tonykoop/kora/cad-recovered-2026-07-04/cad/neck_cnc/neck_cnc_preview.png

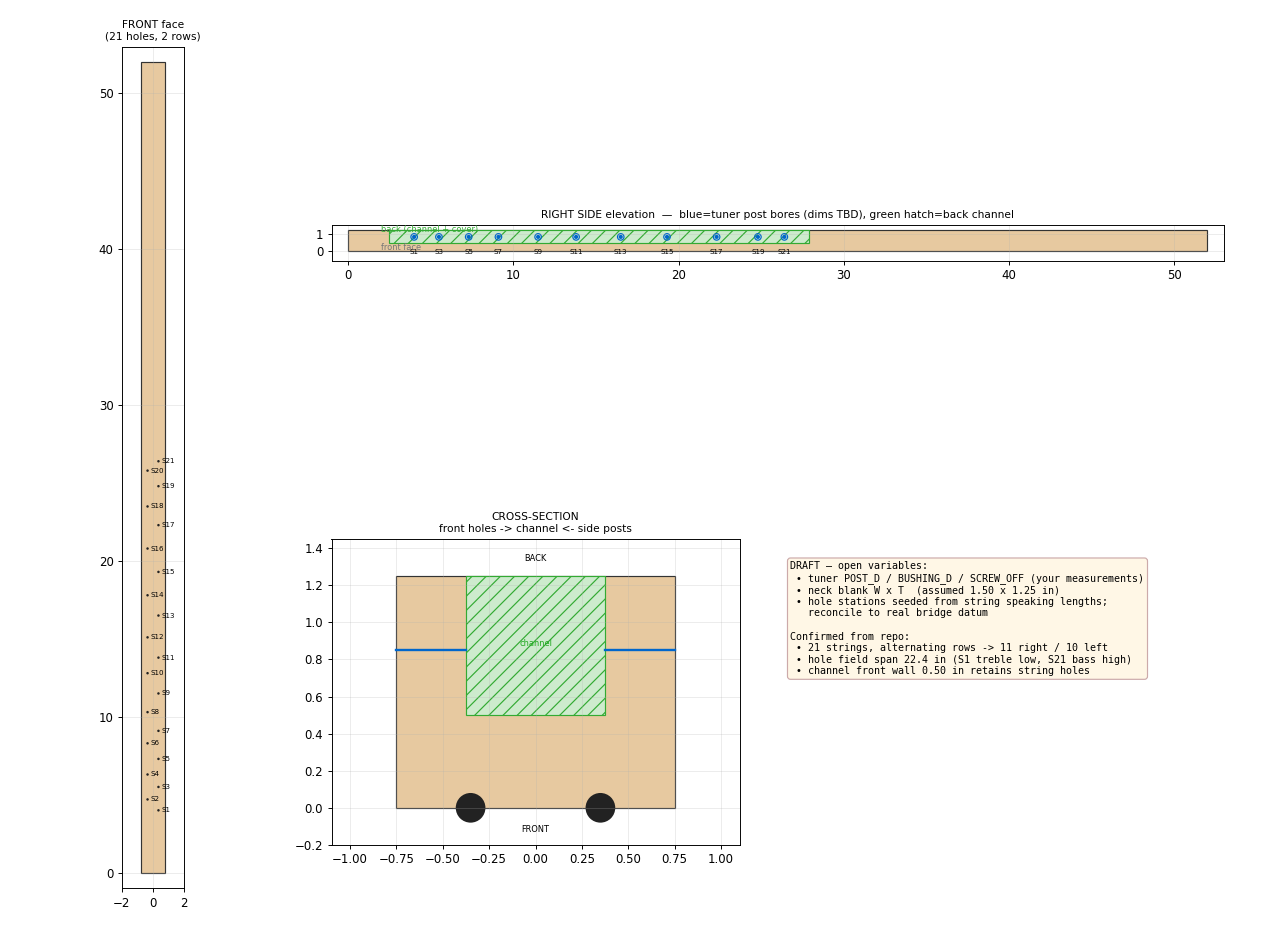
cad-recovered-2026-07-04/cad/neck_cnc/neck_cnc_preview.png
