tonykoop/kora/projects/Large 50” African Kora Style String Instrument Gourd Harp Tribal Folk Decor _ eBay_files/s-l500.jpg

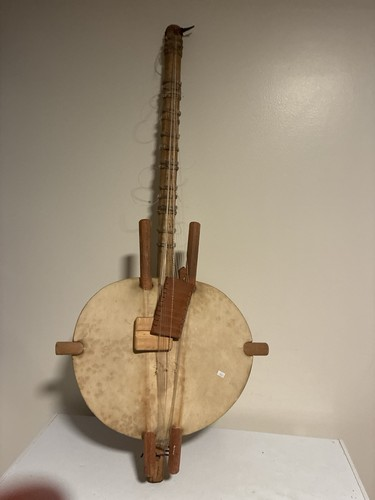
projects/Large 50” African Kora Style String Instrument Gourd Harp Tribal Folk Decor _ eBay_files/s-l500.jpg
