tonykoop/kora/projects/restoration photo album/20260529_142627.jpg

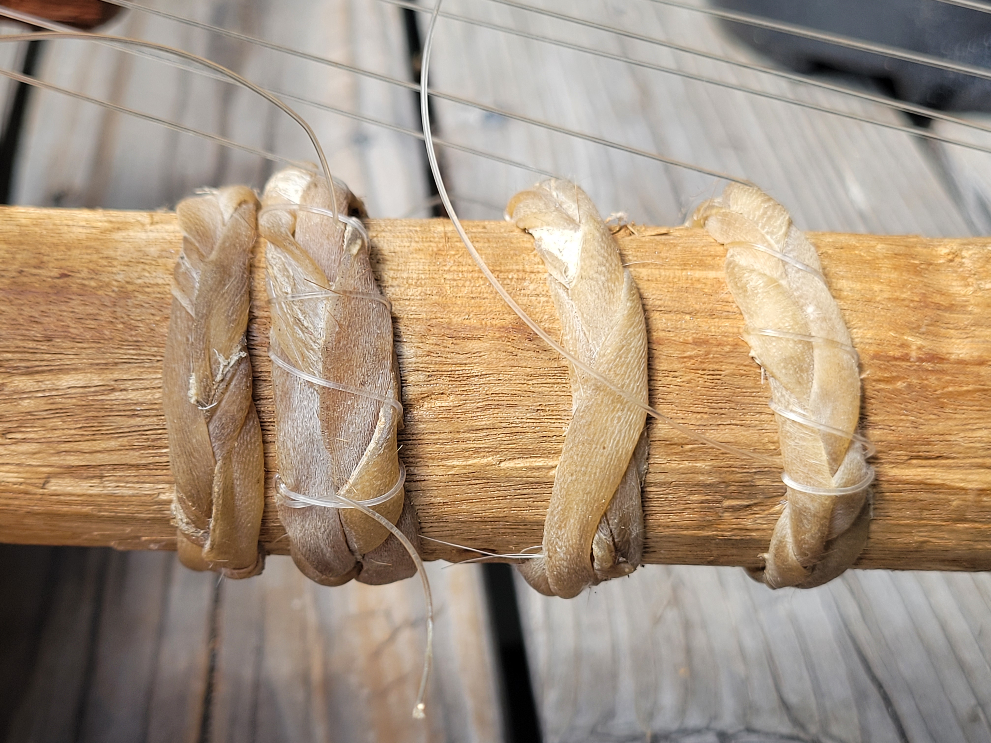
projects/restoration photo album/20260529_142627.jpg
