tonykoop/kora/projects/restoration photo album/20260529_142642.jpg

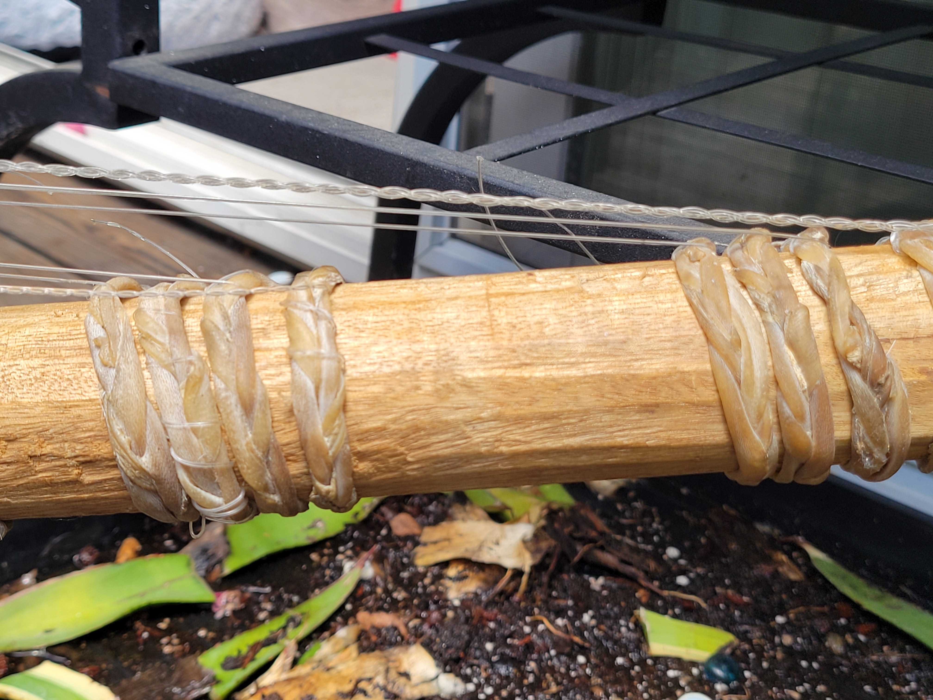
projects/restoration photo album/20260529_142642.jpg
