tonykoop/kora/projects/restoration photo album/20260529_142644.jpg

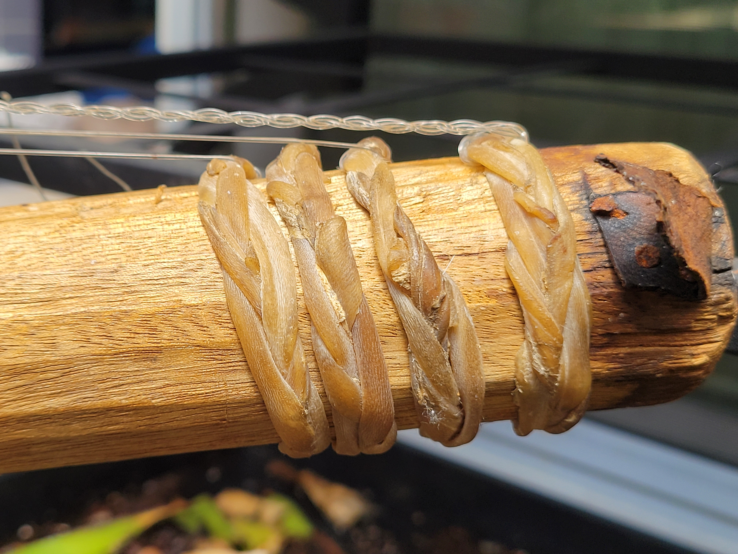
projects/restoration photo album/20260529_142644.jpg
