tonykoop/kora/projects/restoration photo album/20260529_142652.jpg

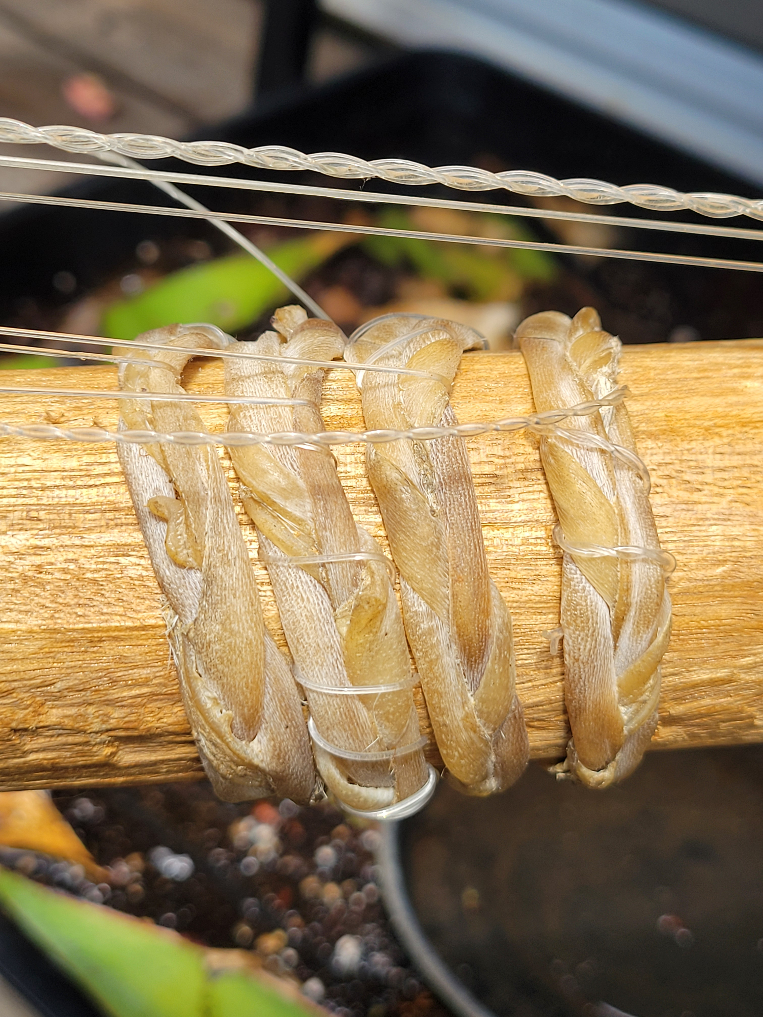
projects/restoration photo album/20260529_142652.jpg
