tonykoop/kora/projects/restoration photo album/20260529_142718.jpg

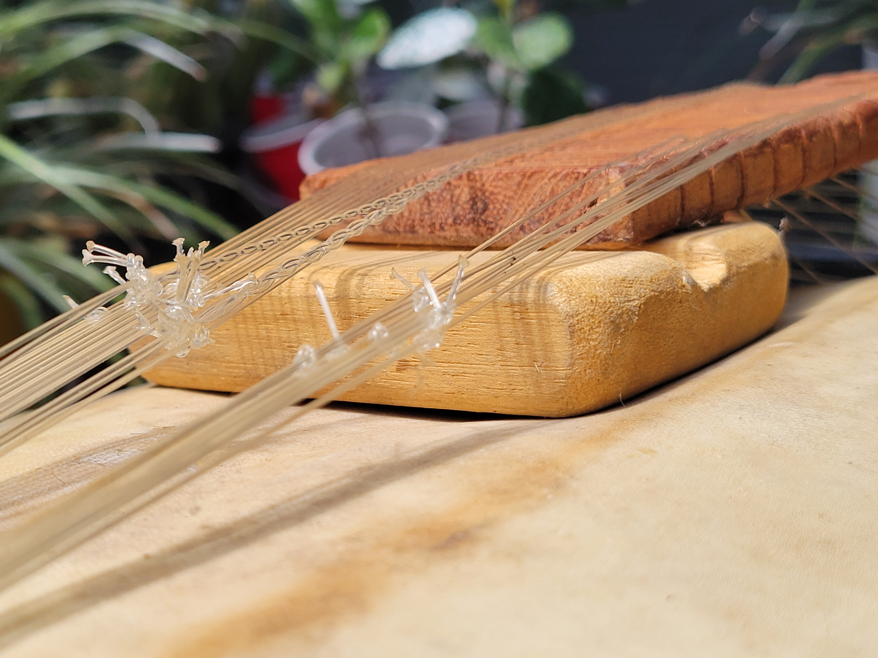
projects/restoration photo album/20260529_142718.jpg
