tonykoop/kora/projects/restoration photo album/20260529_142737.jpg

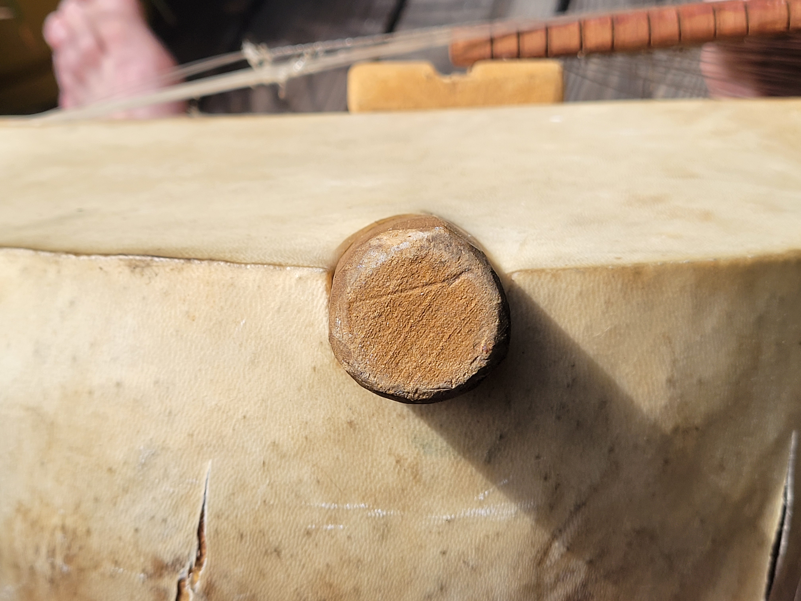
projects/restoration photo album/20260529_142737.jpg
