tonykoop/kora/projects/restoration photo album/20260529_142741.jpg

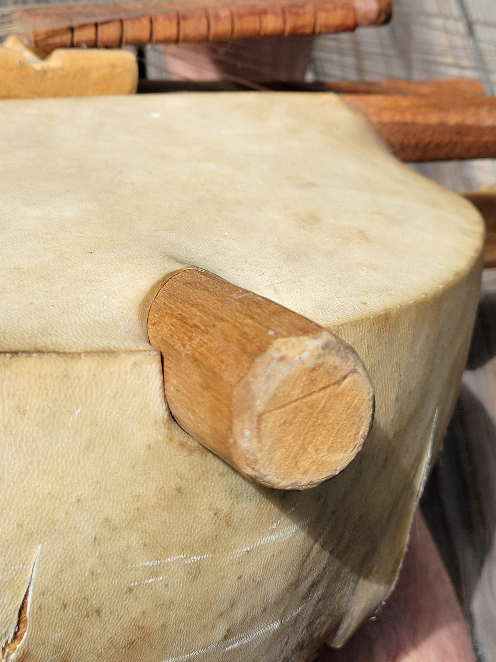
projects/restoration photo album/20260529_142741.jpg
