tonykoop/kora/projects/restoration photo album/20260529_142750.jpg

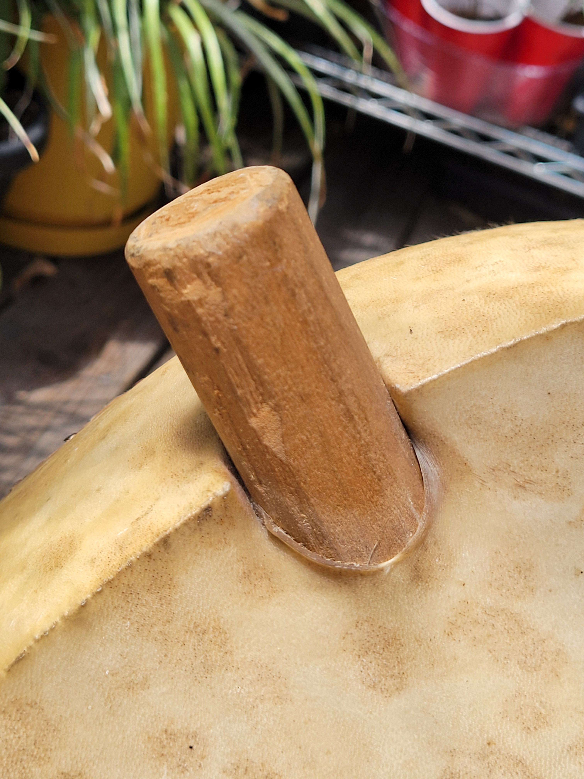
projects/restoration photo album/20260529_142750.jpg
