tonykoop/kora/projects/restoration photo album/20260529_142814.jpg

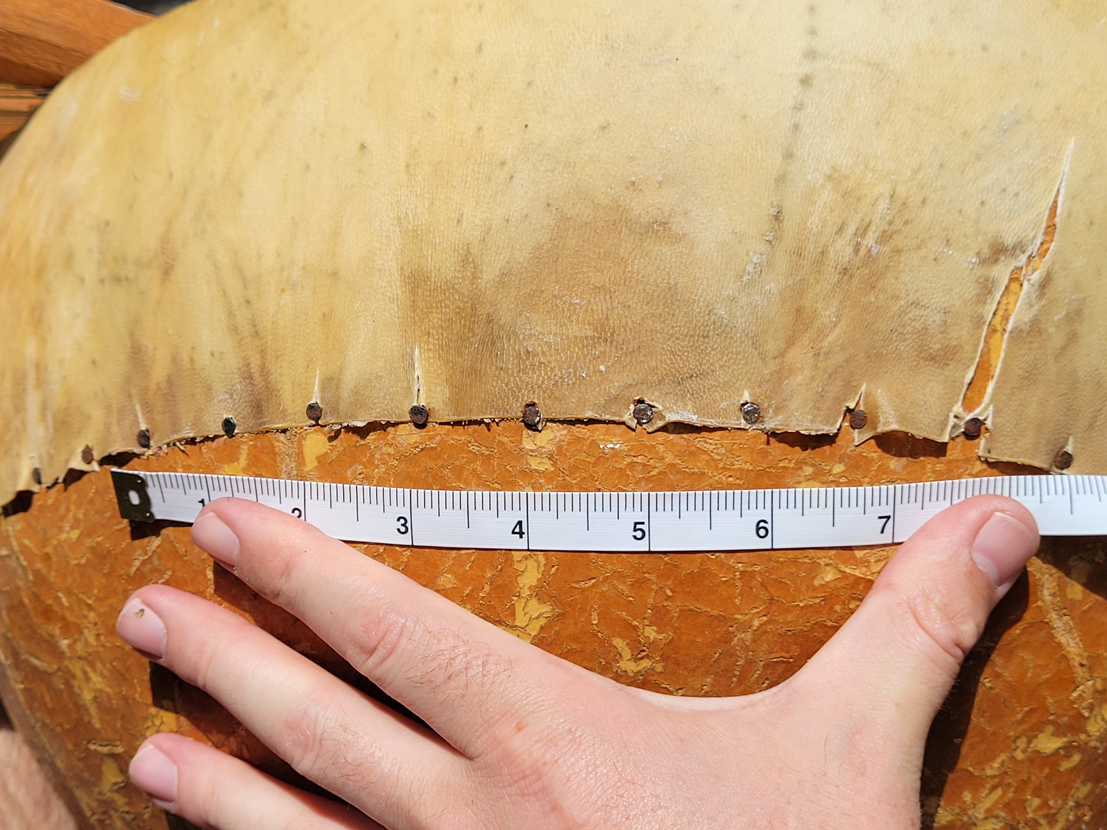
projects/restoration photo album/20260529_142814.jpg
