tonykoop/kora/projects/restoration photo album/20260529_142840.jpg

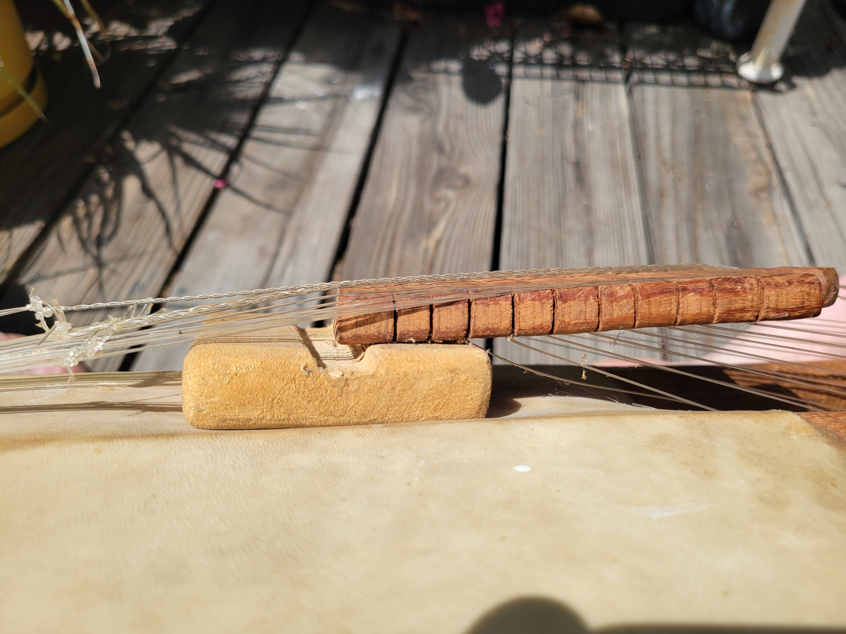
projects/restoration photo album/20260529_142840.jpg
