tonykoop/kora/projects/restoration photo album/20260529_142852.jpg

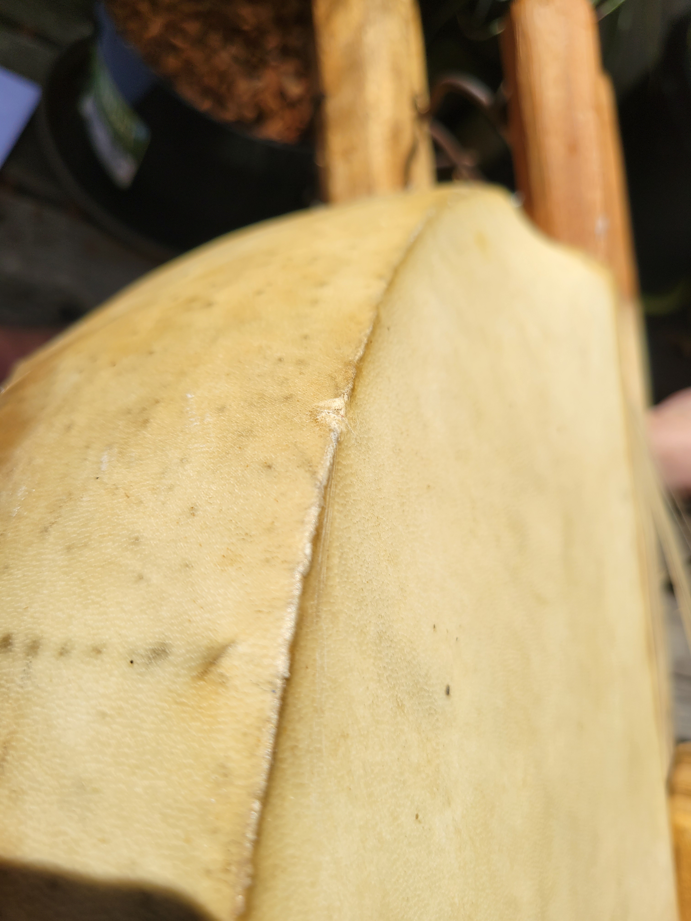
projects/restoration photo album/20260529_142852.jpg
