tonykoop/kora/projects/restoration photo album/20260529_142935.jpg

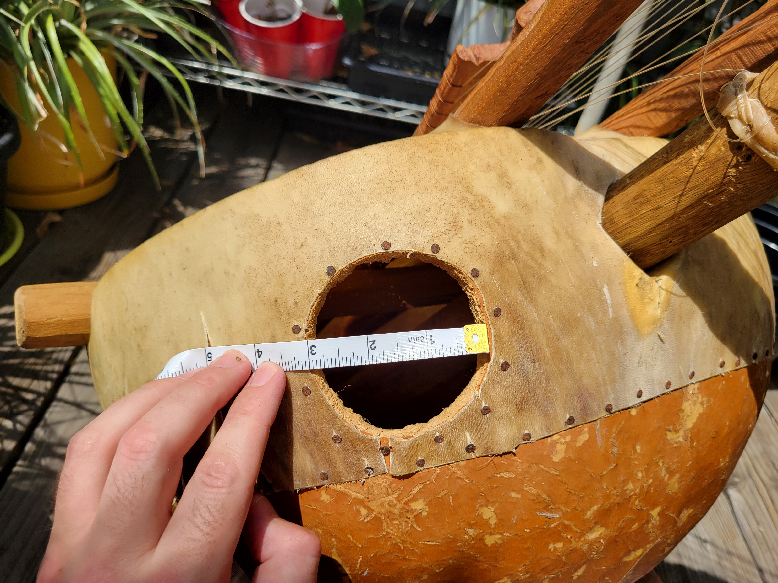
projects/restoration photo album/20260529_142935.jpg
