tonykoop/kora/projects/restoration photo album/20260529_143312.jpg

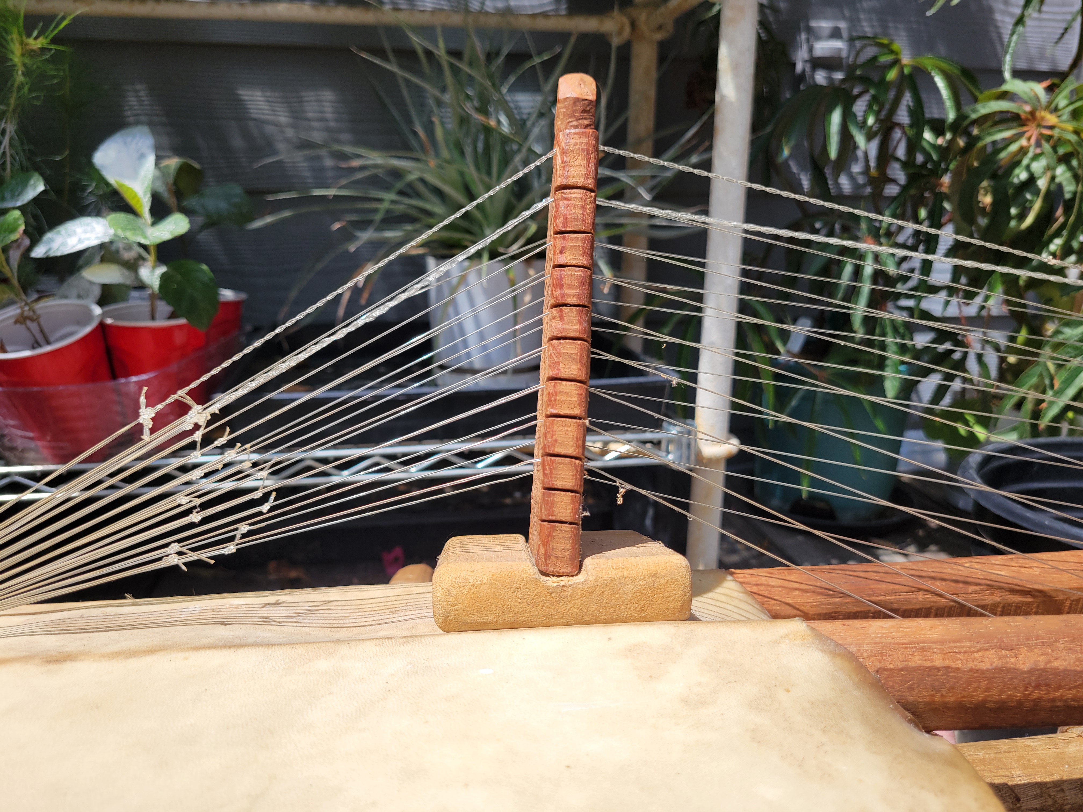
projects/restoration photo album/20260529_143312.jpg
