tonykoop/kora/cad/KOR-000-BridgePad.SLDPRT

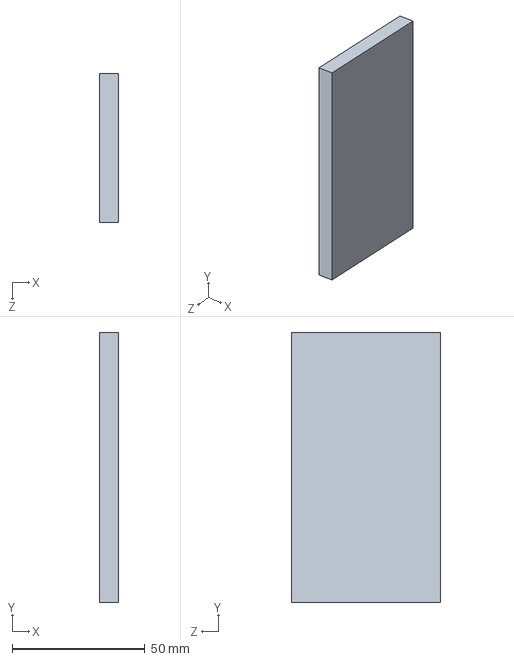
[picture p44: CAD file, 2026-07-09]
cad/KOR-000-BridgePad.SLDPRT
6.98 x 101.6 x 55.9 mm
