tonykoop/kora/cad/neck2_cnc/KOR-NECK-GlueUpV3.SLDPRT

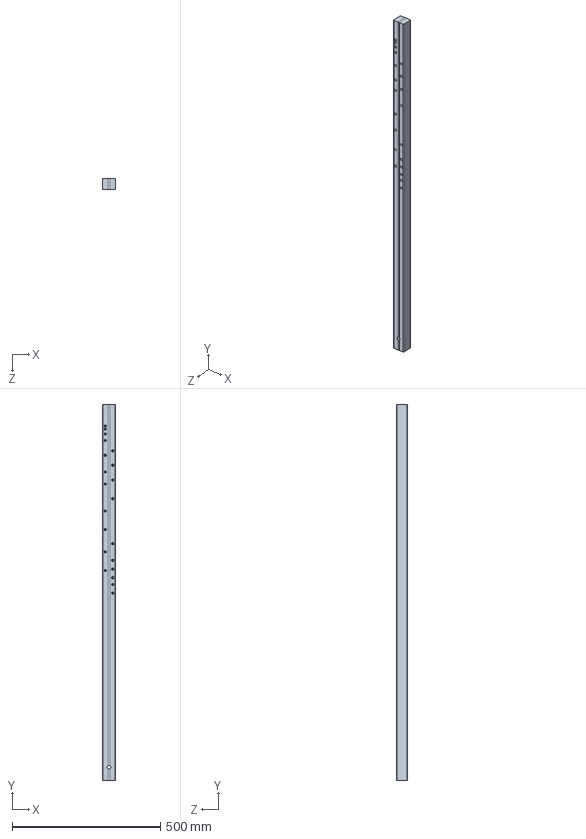
[picture p45: CAD file, 2026-07-09]
cad/neck2_cnc/KOR-NECK-GlueUpV3.SLDPRT
44.5 x 1270.0 x 38.1 mm
