tonykoop/kora/cad-recovered-2026-07-04/cad/BrassRod3-16.SLDPRT

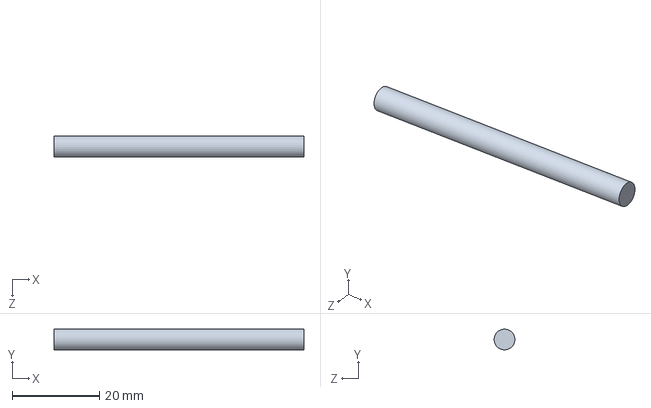
[picture p46: CAD file, 2026-07-09]
cad-recovered-2026-07-04/cad/BrassRod3-16.SLDPRT
57.1 x 4.76 x 4.76 mm
