tonykoop/kora/cad/Musiclily Pro 14mm bass string ferrule.SLDPRT

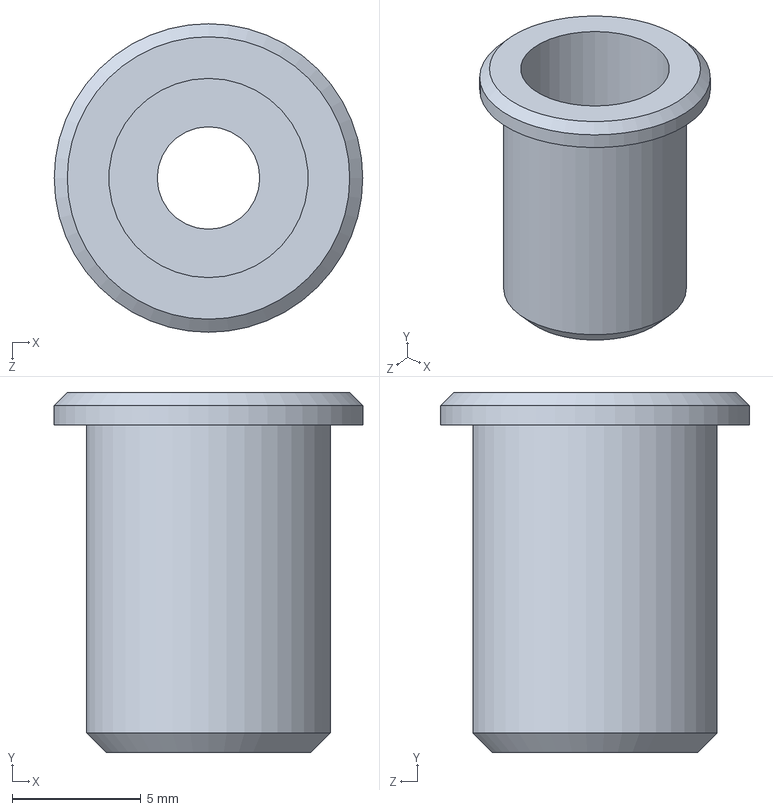
[picture p47: CAD file, 2026-07-09]
cad/Musiclily Pro 14mm bass string ferrule.SLDPRT
12.0 x 14.0 x 12.0 mm
