tonykoop/kora/cad/neck2_cnc/KOR-NECK-CENTER.SLDPRT

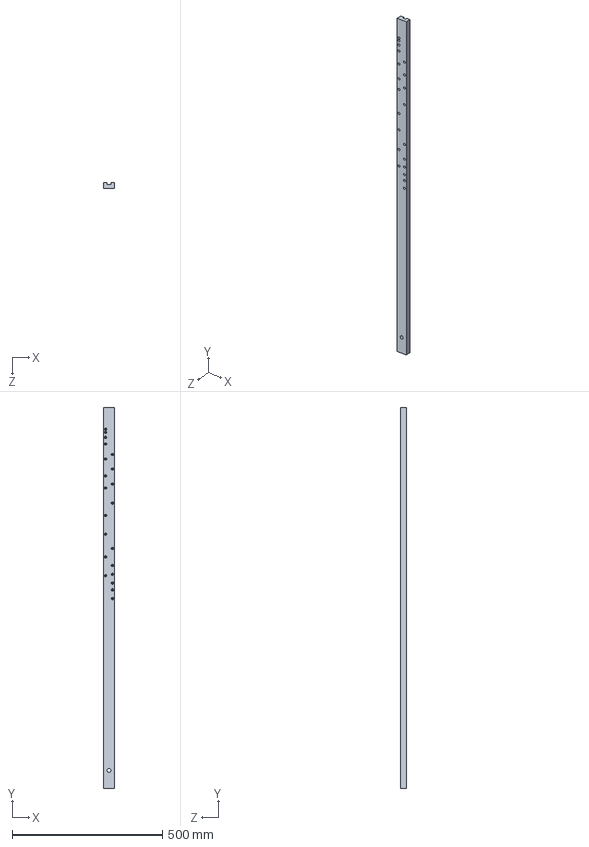
[picture p48: CAD file, 2026-07-09]
cad/neck2_cnc/KOR-NECK-CENTER.SLDPRT
38.1 x 1270.0 x 19.1 mm
