tonykoop/kora/cad-recovered-from-stash-20260518/cad/KOR-000-Gourd.SLDPRT

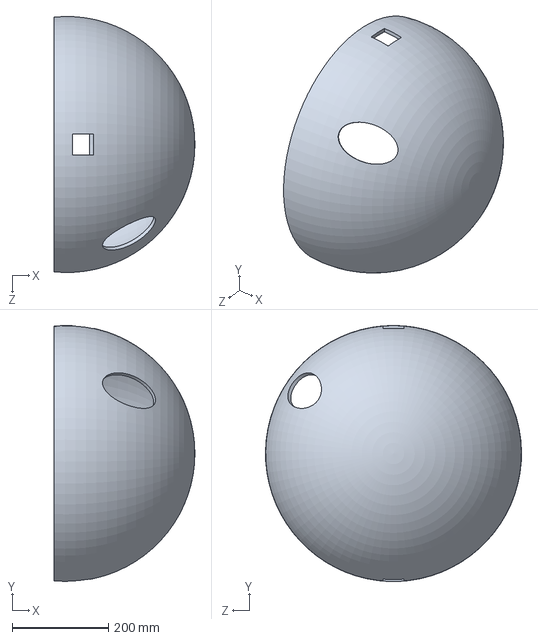
[picture p49: CAD file, 2026-05-31]
cad-recovered-from-stash-20260518/cad/KOR-000-Gourd.SLDPRT
293.4 x 533.4 x 533.2 mm
