tonykoop/kora/cad/KOR-000-Membrane.SLDPRT

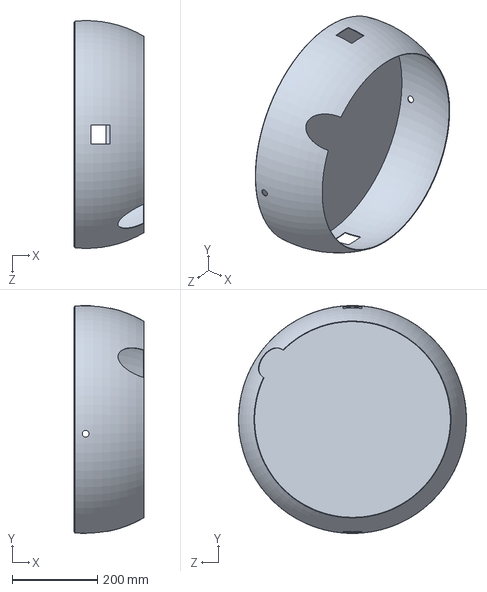
[picture p50: CAD file, 2026-07-09]
cad/KOR-000-Membrane.SLDPRT
163.6 x 536.4 x 535.9 mm
