tonykoop/kora/cad/neck2_cnc/KOR-NECK-SIDE.SLDPRT

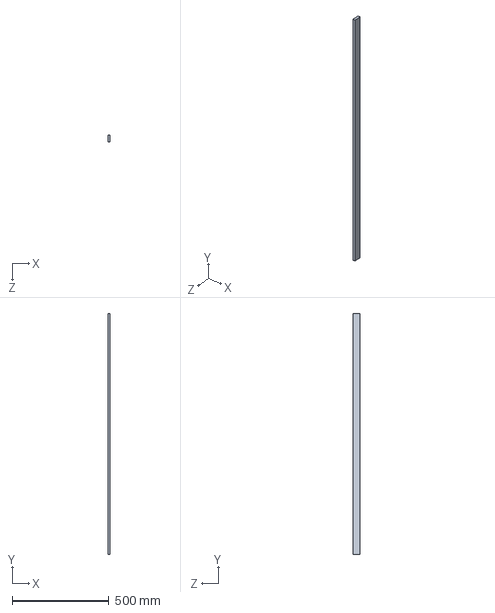
[picture p51: CAD file, 2026-07-07]
cad/neck2_cnc/KOR-NECK-SIDE.SLDPRT
12.7 x 1244.6 x 38.1 mm
