tonykoop/kora/cad-recovered-2026-07-04/cad/KOR-000-LaminateBottom.SLDPRT

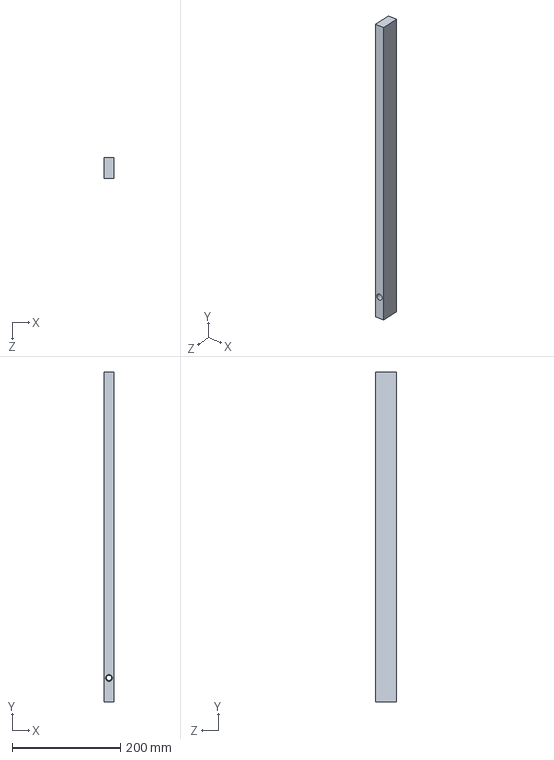
[picture p52: CAD file, 2026-07-09]
cad-recovered-2026-07-04/cad/KOR-000-LaminateBottom.SLDPRT
19.1 x 609.6 x 38.1 mm
