tonykoop/kora/cad/neck2_cnc/KOR-STRING-END.SLDPRT

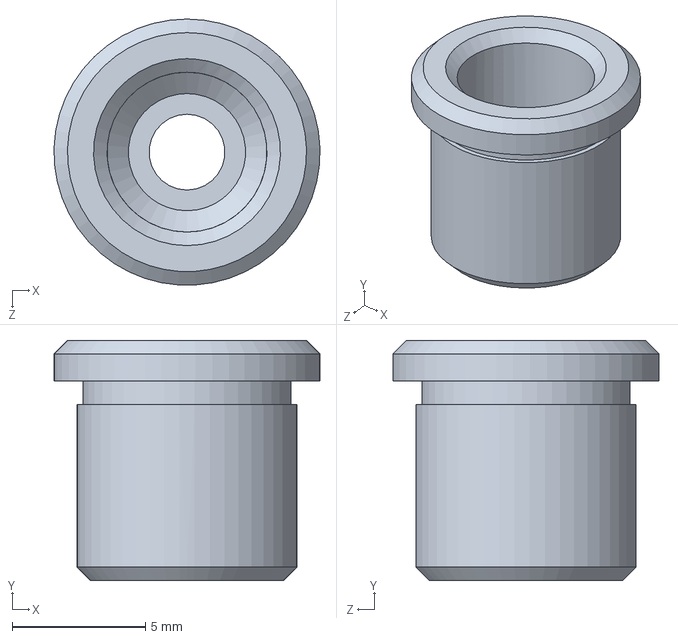
[picture p53: CAD file, 2026-07-07]
cad/neck2_cnc/KOR-STRING-END.SLDPRT
9.98 x 9.02 x 9.97 mm
