tonykoop/kora/cad/KOR-000-Bridge.SLDPRT

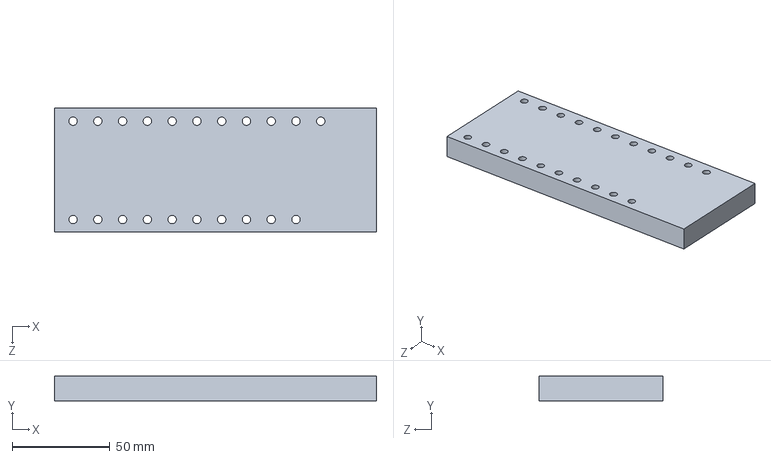
[picture p54: CAD file, 2026-07-09]
cad/KOR-000-Bridge.SLDPRT
165.1 x 12.7 x 63.5 mm
