tonykoop/kora/cad-recovered-2026-07-04/cad/KOR-000-Neck.SLDPRT

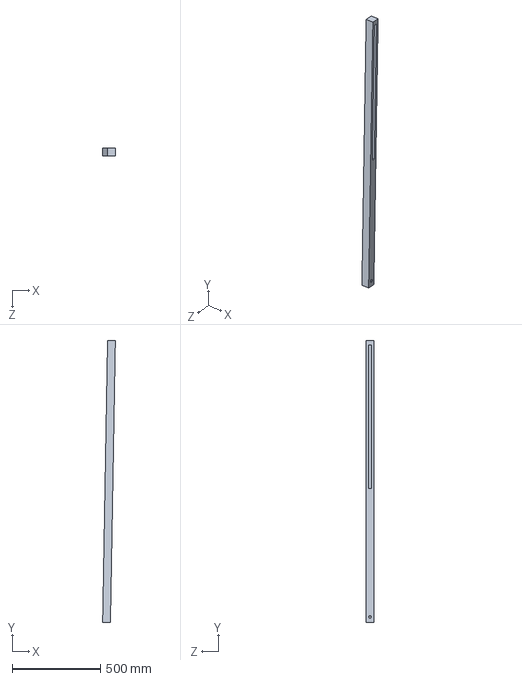
[picture p55: CAD file, 2026-07-07]
cad-recovered-2026-07-04/cad/KOR-000-Neck.SLDPRT
72.4 x 1600.4 x 44.5 mm
