tonykoop/kora/cad/KOR-000-Crossbar.SLDPRT

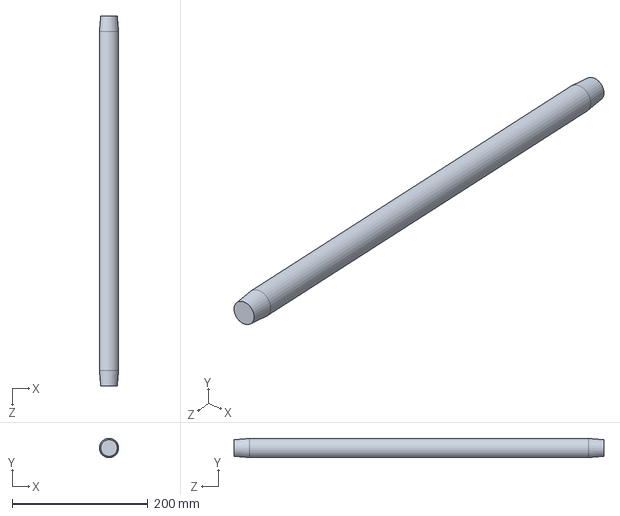
[picture p56: CAD file, 2026-07-09]
cad/KOR-000-Crossbar.SLDPRT
28.6 x 28.4 x 546.1 mm
