tonykoop/kora/cad-recovered-from-stash-20260518/cad/KOR-000-Crossbar.SLDPRT

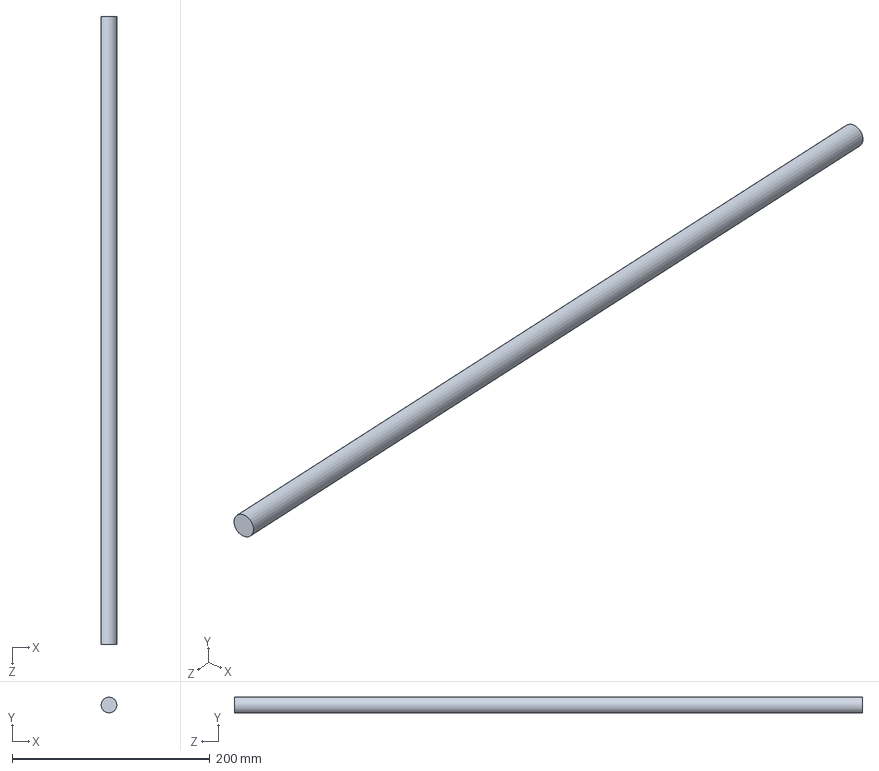
[picture p57: CAD file, 2026-05-31]
cad-recovered-from-stash-20260518/cad/KOR-000-Crossbar.SLDPRT
15.9 x 15.8 x 635.0 mm
