tonykoop/kora/cad/Musiclily Pro 25-5mm bass string ferrule.SLDPRT

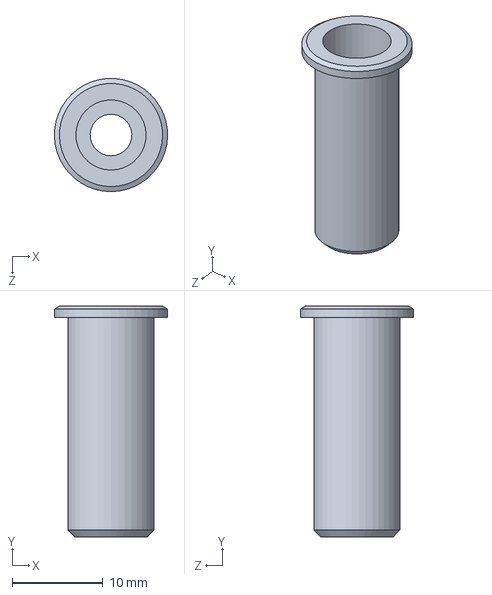
[picture p58: CAD file, 2026-07-09]
cad/Musiclily Pro 25-5mm bass string ferrule.SLDPRT
12.5 x 25.5 x 12.5 mm
