tonykoop/kora/projects/restoration photo album/20260529_141125.jpg

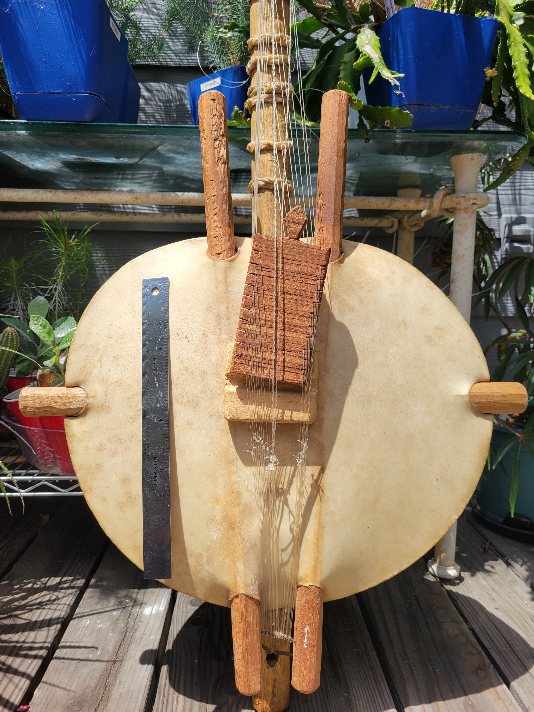
projects/restoration photo album/20260529_141125.jpg
