tonykoop/kora/projects/restoration photo album/20260529_141643.jpg

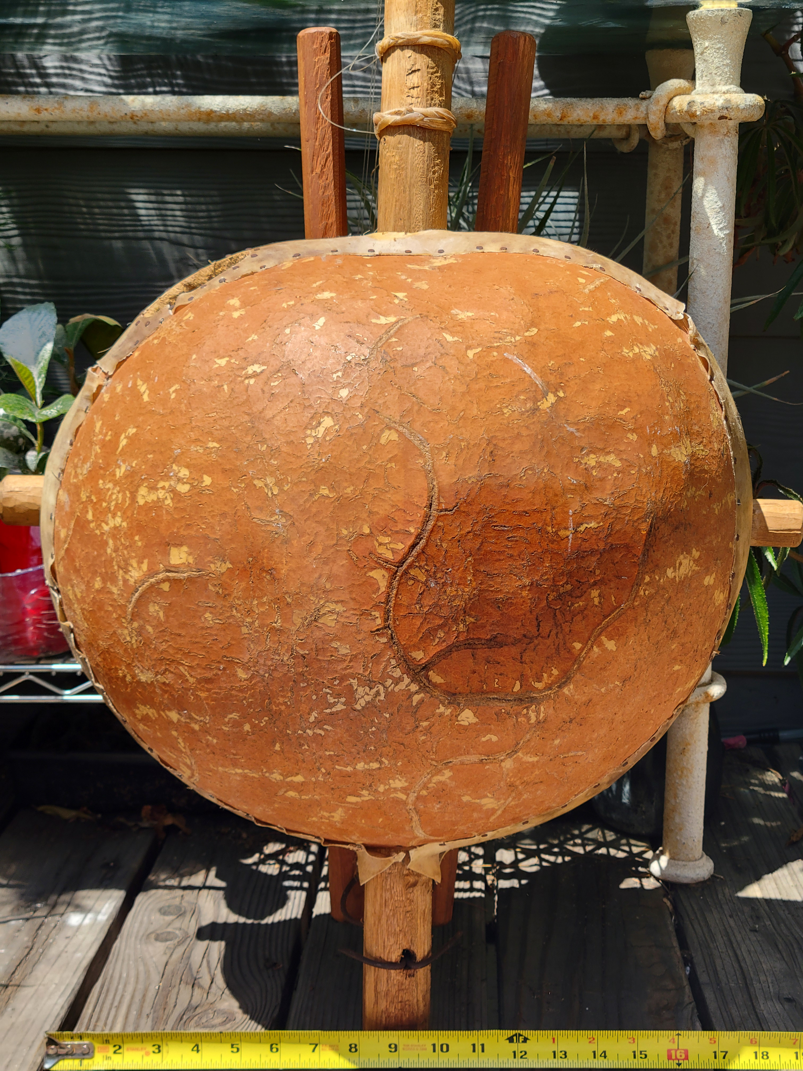
projects/restoration photo album/20260529_141643.jpg
