tonykoop/kora/projects/restoration photo album/20260529_142139.jpg

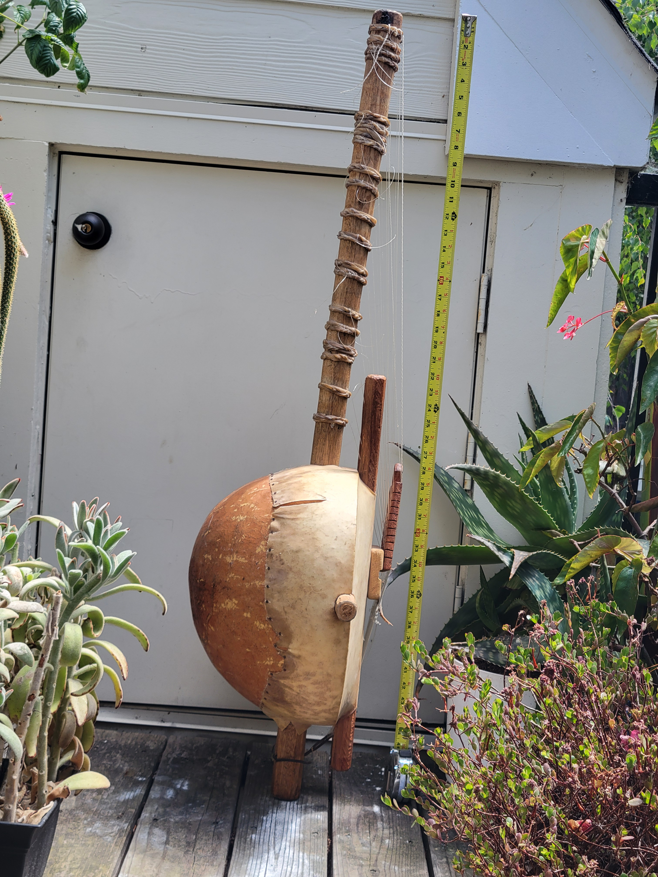
projects/restoration photo album/20260529_142139.jpg
