tonykoop/kora/projects/restoration photo album/20260529_142207.jpg

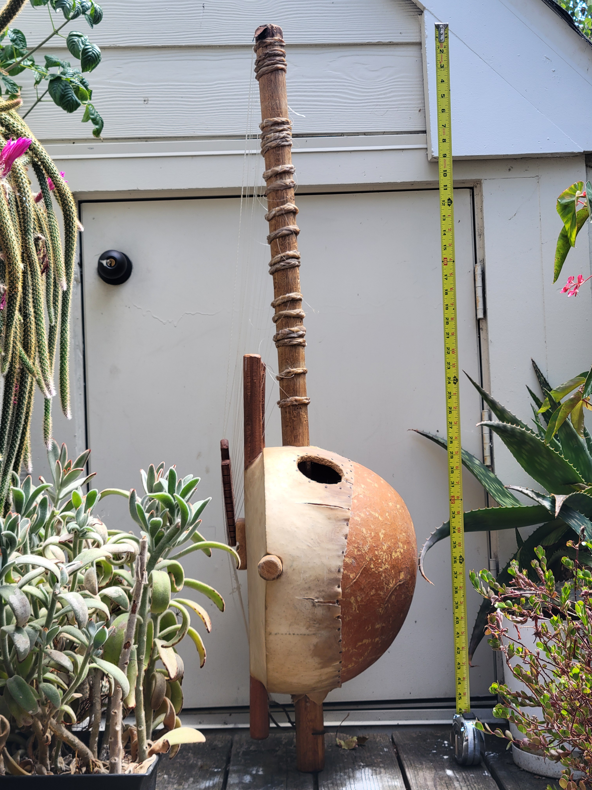
projects/restoration photo album/20260529_142207.jpg
