tonykoop/kora/projects/restoration photo album/20260529_142250.jpg

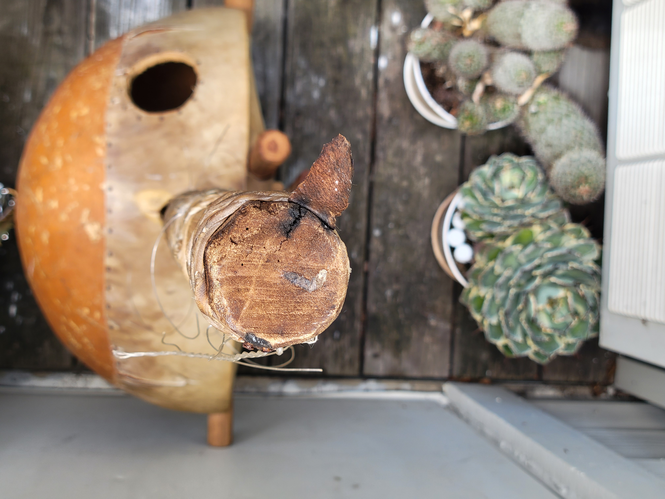
projects/restoration photo album/20260529_142250.jpg
