tonykoop/kora/projects/restoration photo album/20260529_142322.jpg

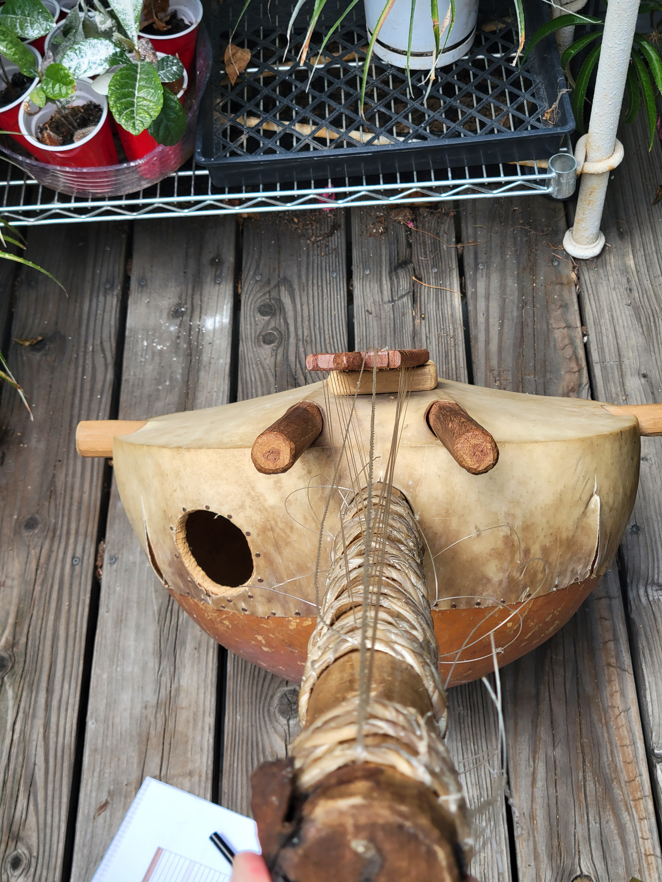
projects/restoration photo album/20260529_142322.jpg
