tonykoop/kora/projects/restoration photo album/20260529_142325.jpg

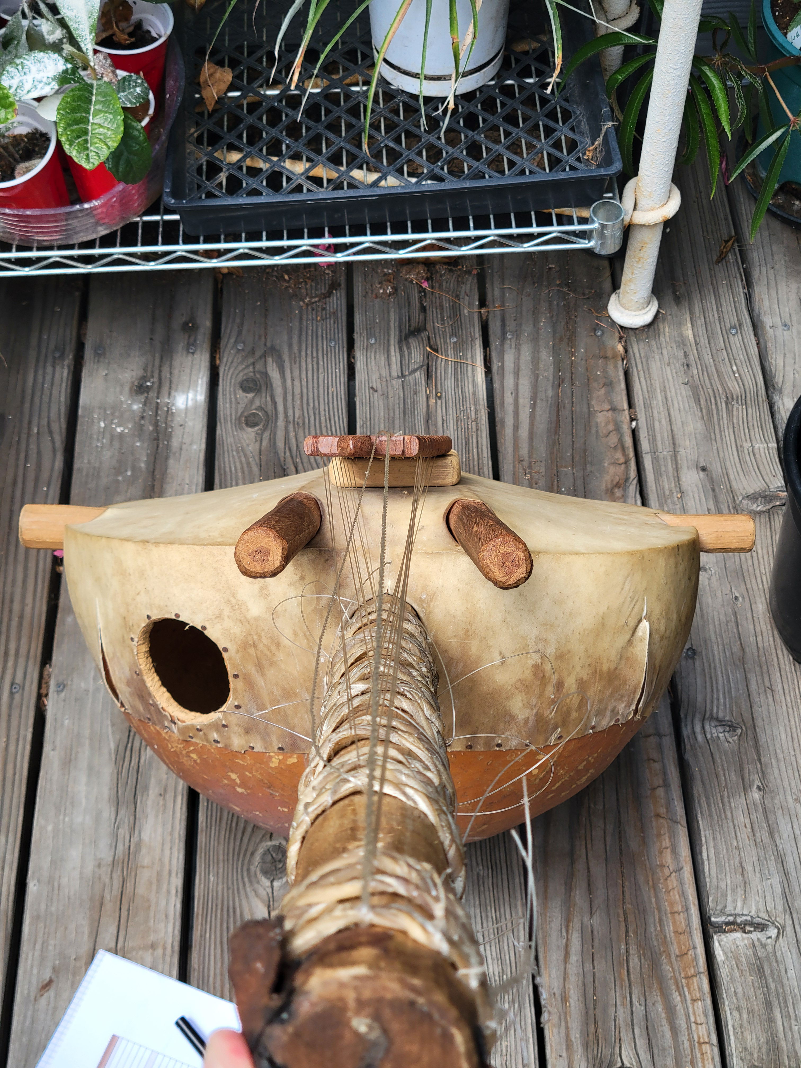
projects/restoration photo album/20260529_142325.jpg
