tonykoop/kora/projects/restoration photo album/20260529_142418.jpg

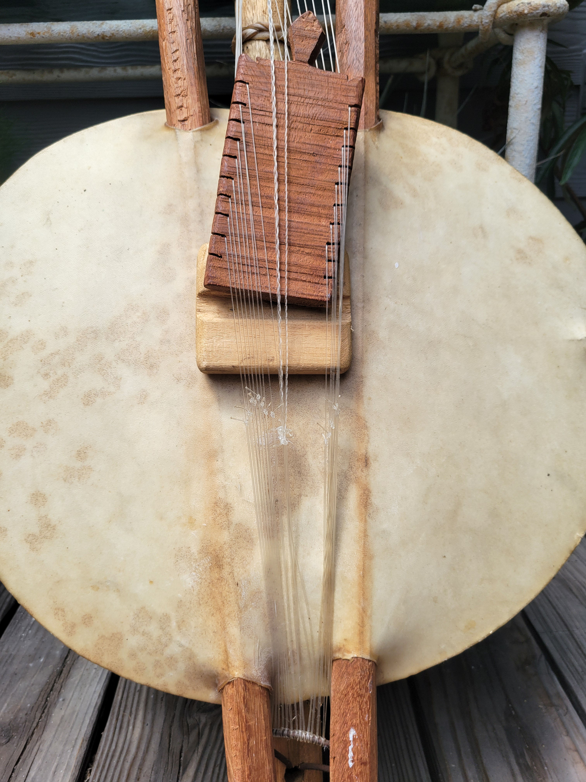
projects/restoration photo album/20260529_142418.jpg
