tonykoop/kora/projects/restoration photo album/20260529_142550.jpg

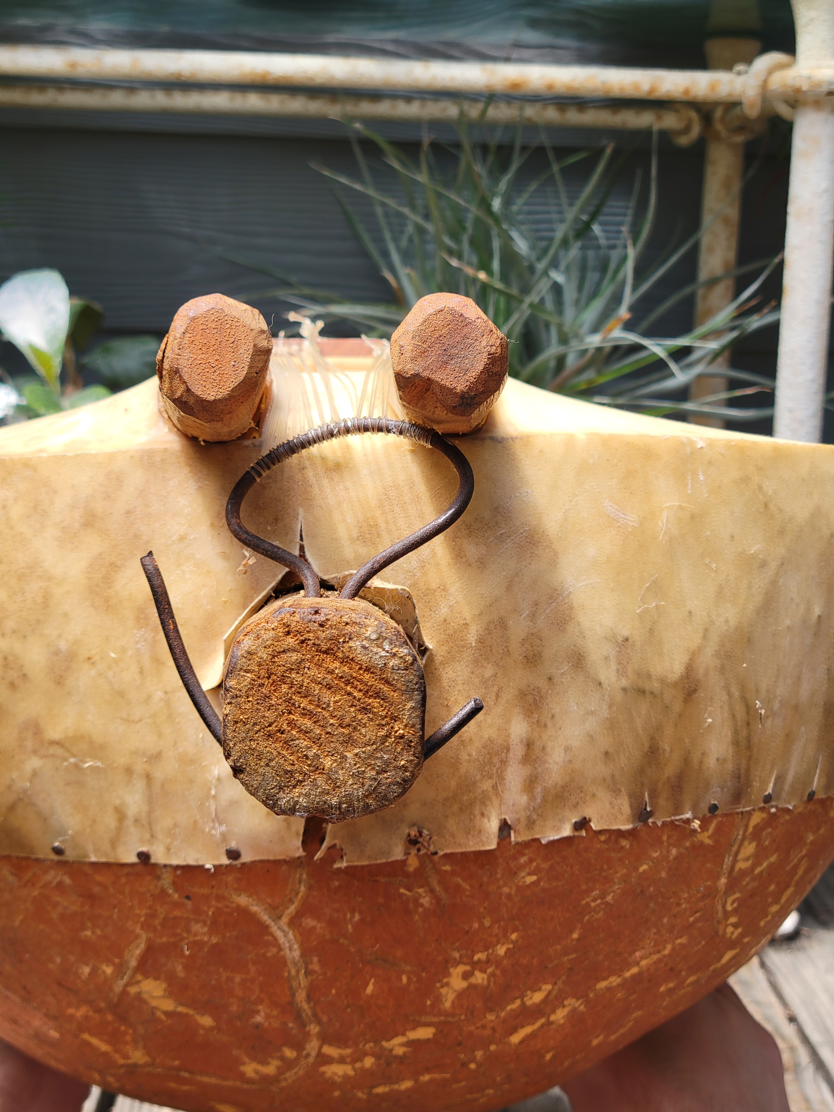
projects/restoration photo album/20260529_142550.jpg
