tonykoop/kora/projects/restoration photo album/20260529_142557.jpg

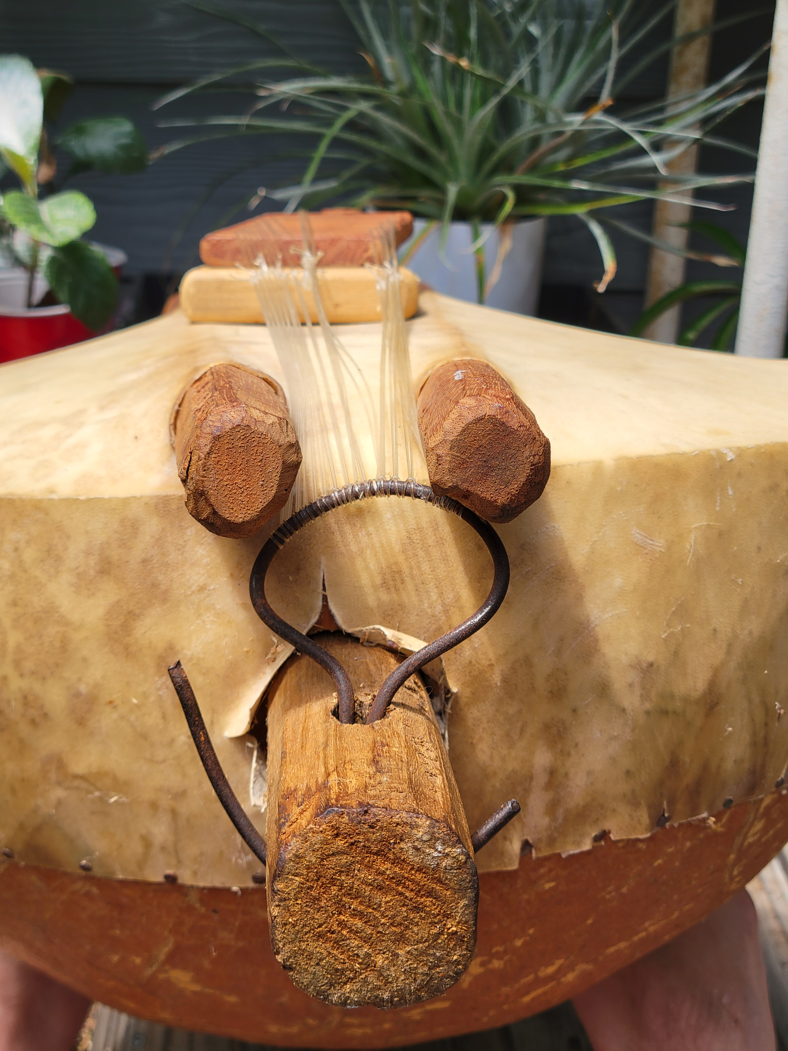
projects/restoration photo album/20260529_142557.jpg
