tonykoop/kora/projects/restoration photo album/20260529_143001.jpg

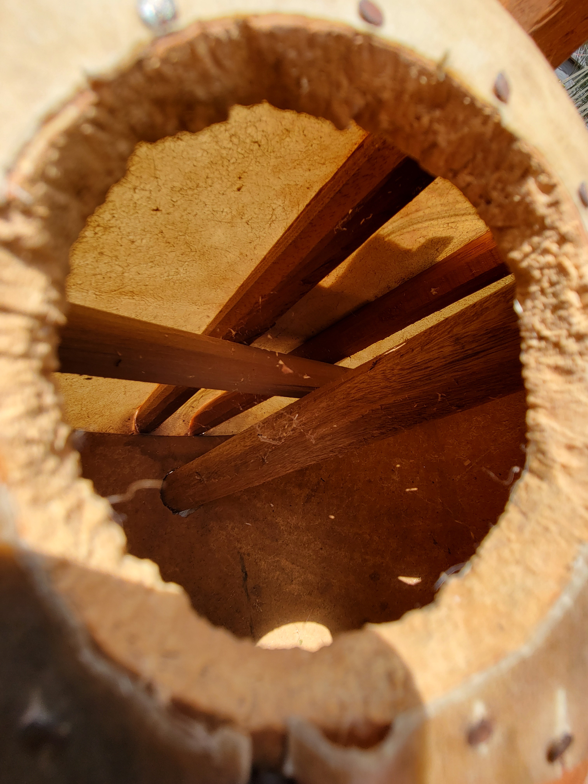
projects/restoration photo album/20260529_143001.jpg
