tonykoop/kora/projects/restoration photo album/20260529_143243.jpg

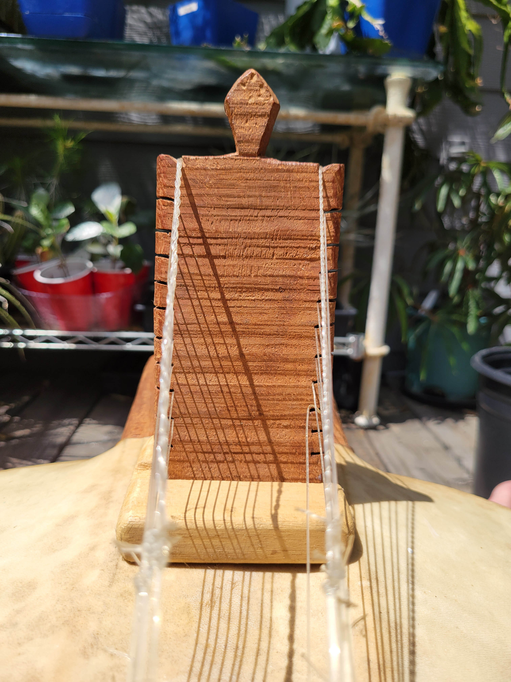
projects/restoration photo album/20260529_143243.jpg
