tonykoop/kora/projects/new kora build/20260530_205213.jpg

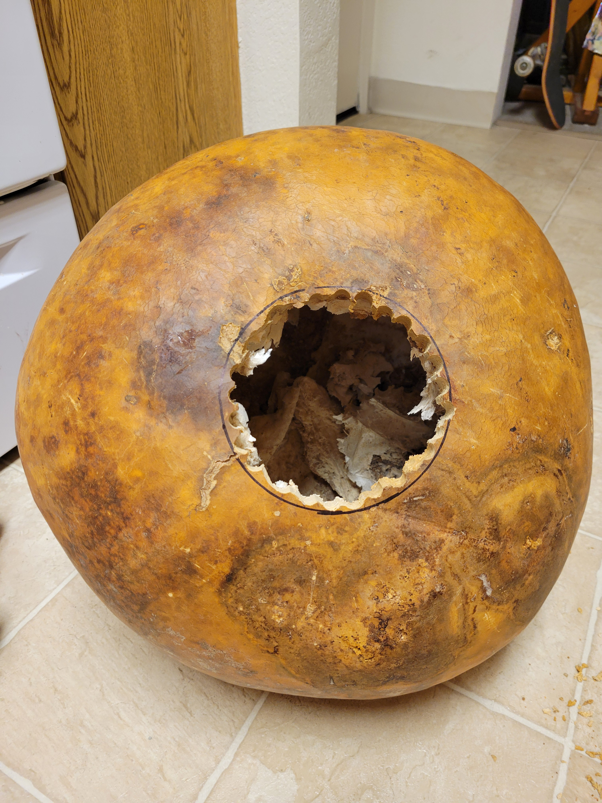
projects/new kora build/20260530_205213.jpg
