tonykoop/kora/projects/new kora build/20260530_205236.jpg

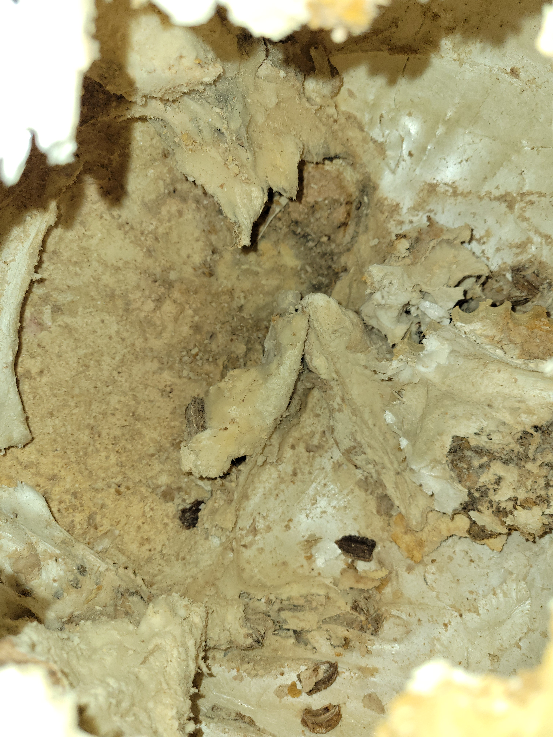
projects/new kora build/20260530_205236.jpg
