tonykoop/kora/projects/new kora build/20260530_210333.jpg

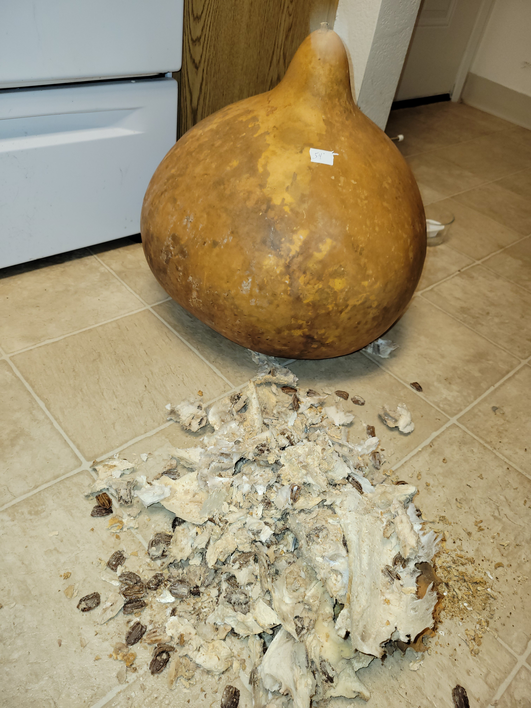
projects/new kora build/20260530_210333.jpg
