tonykoop/kora/projects/new kora build/20260530_212537.jpg

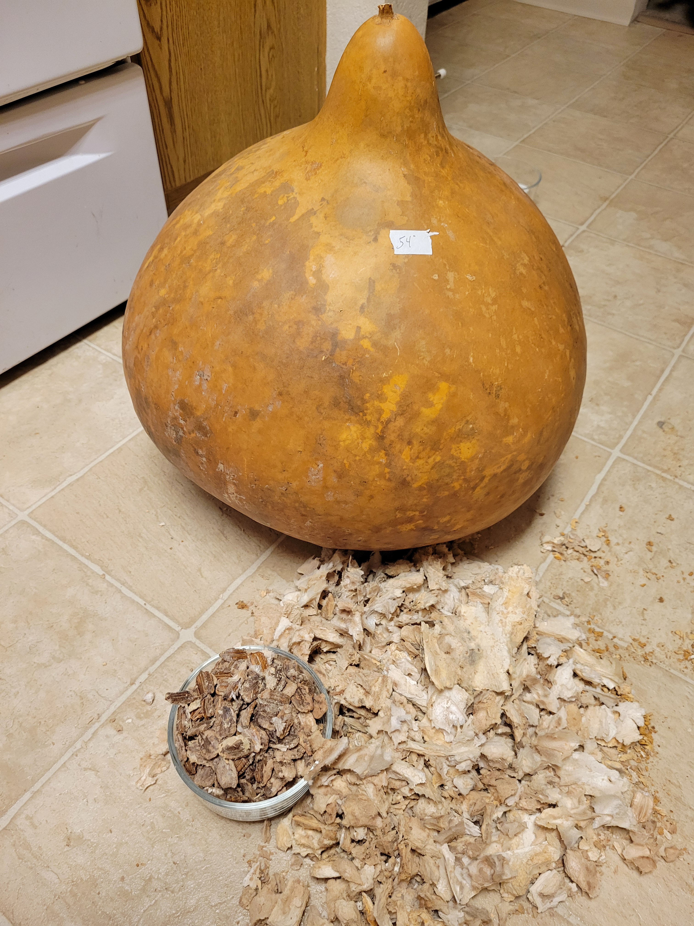
projects/new kora build/20260530_212537.jpg
